xavierbasc/dm50/3d/render01.png

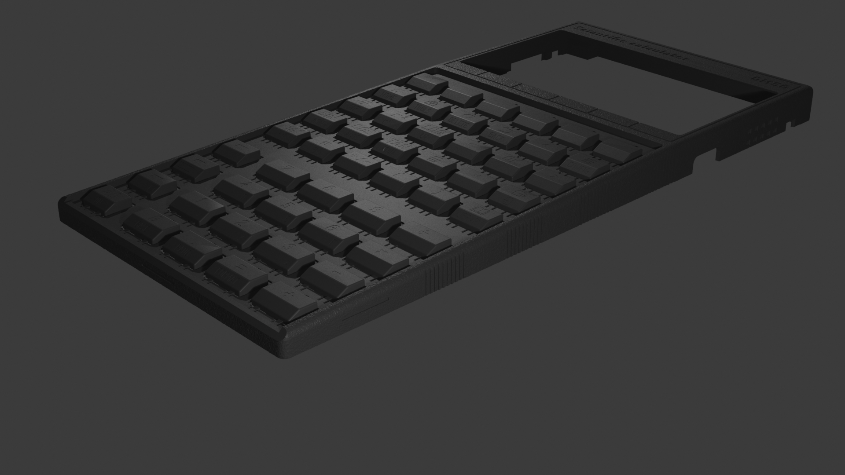
3d/render01.png
