xavierbasc/dm50/docs/img/AT25SF641.jpeg

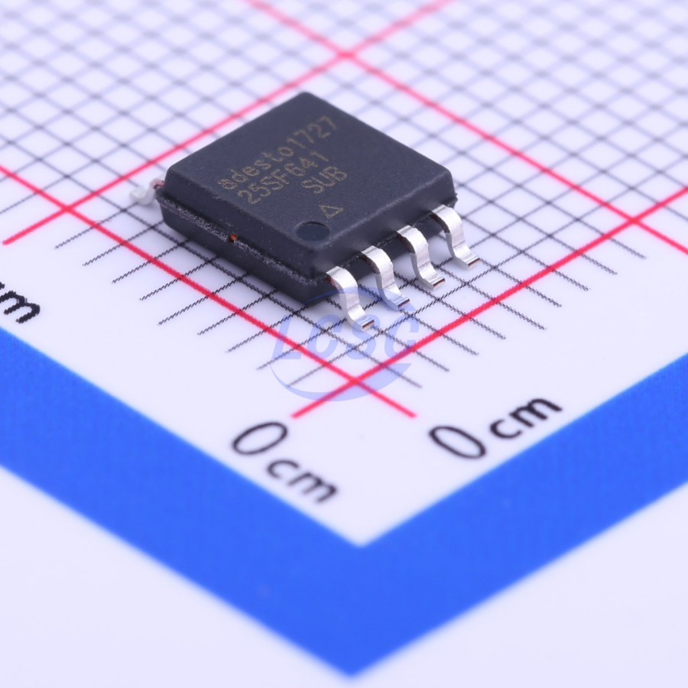
docs/img/AT25SF641.jpeg
