xavierbasc/dm50/docs/img/case3d.png

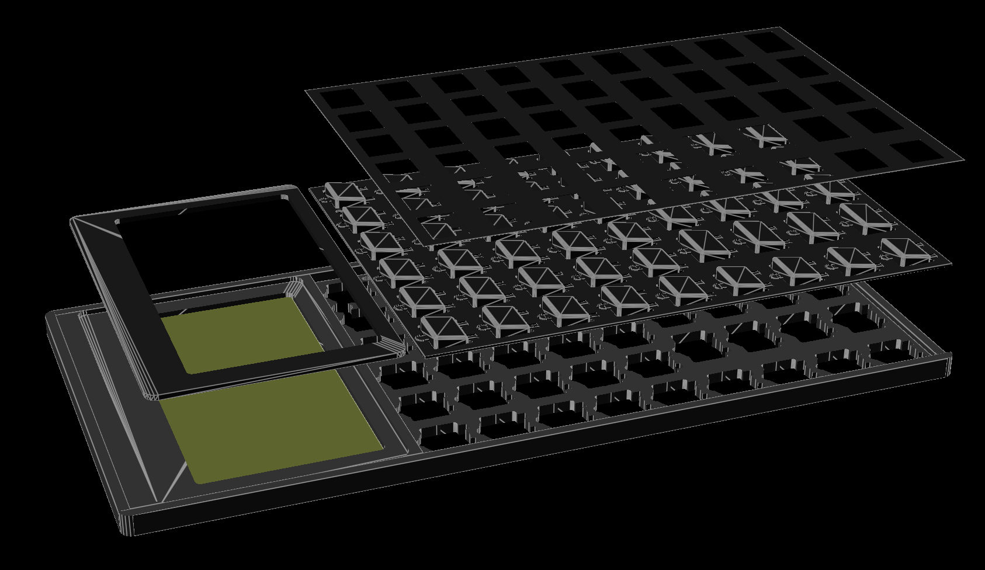
docs/img/case3d.png
