xavierbasc/dm50/docs/img/DM50_PCB.png

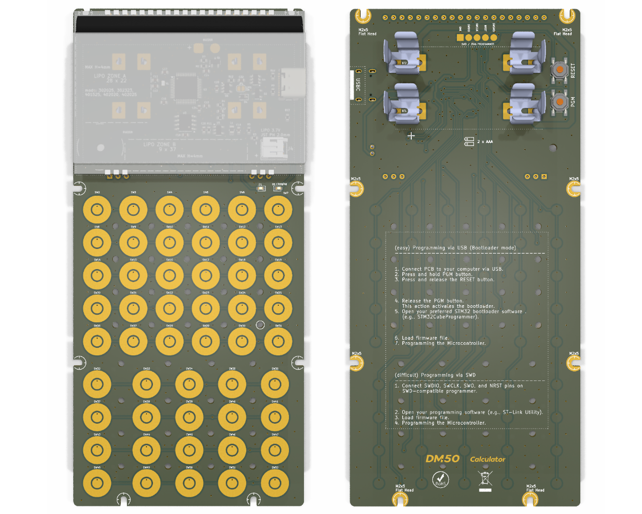
docs/img/DM50_PCB.png
