xavierbasc/dm50/docs/img/FFab.png

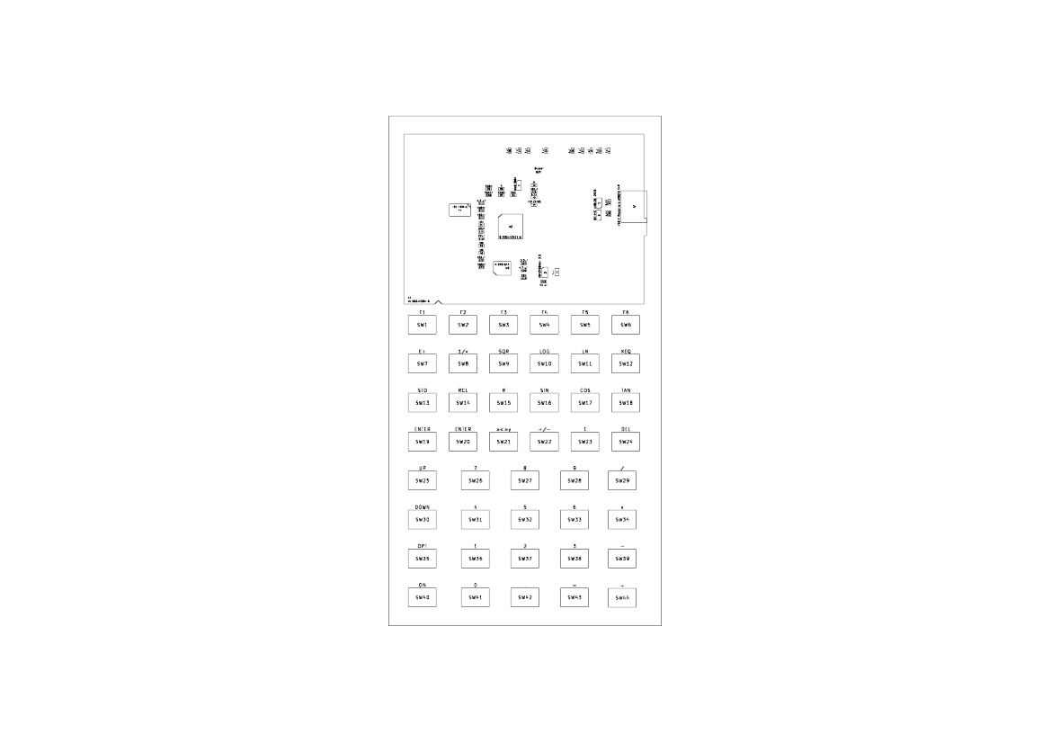
docs/img/FFab.png
