xavierbasc/dm50/docs/img/keyboard_b.png

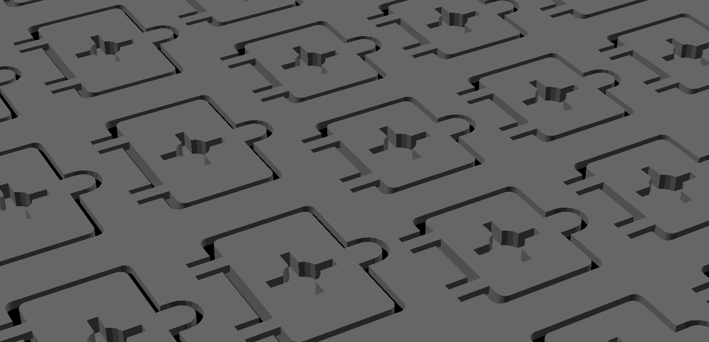
docs/img/keyboard_b.png
