xavierbasc/dm50/docs/img/PCB_3D_back.png

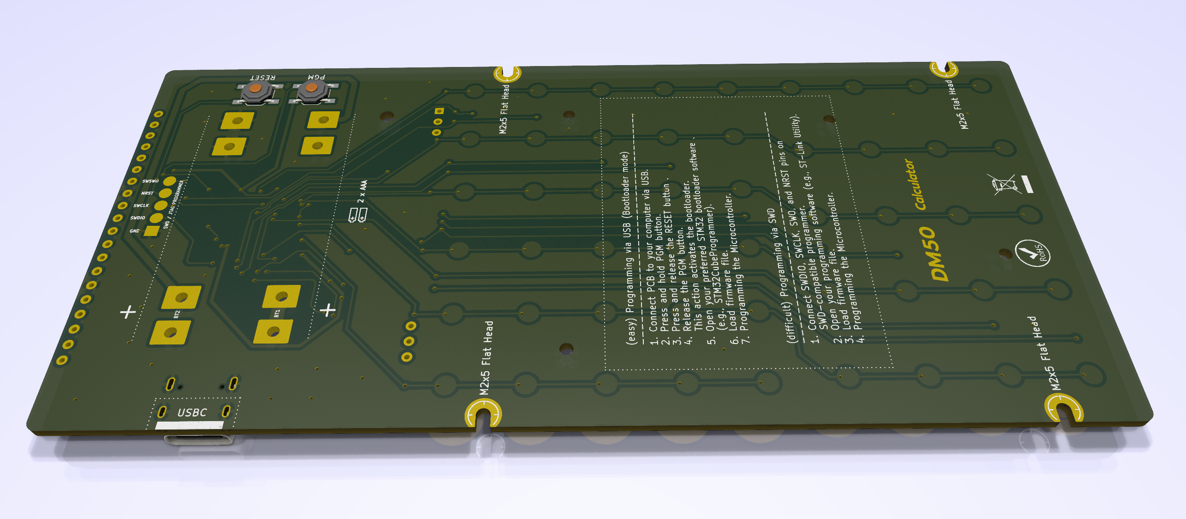
docs/img/PCB_3D_back.png
