xavierbasc/dm50/docs/pdf/PCB/FFab.pdf

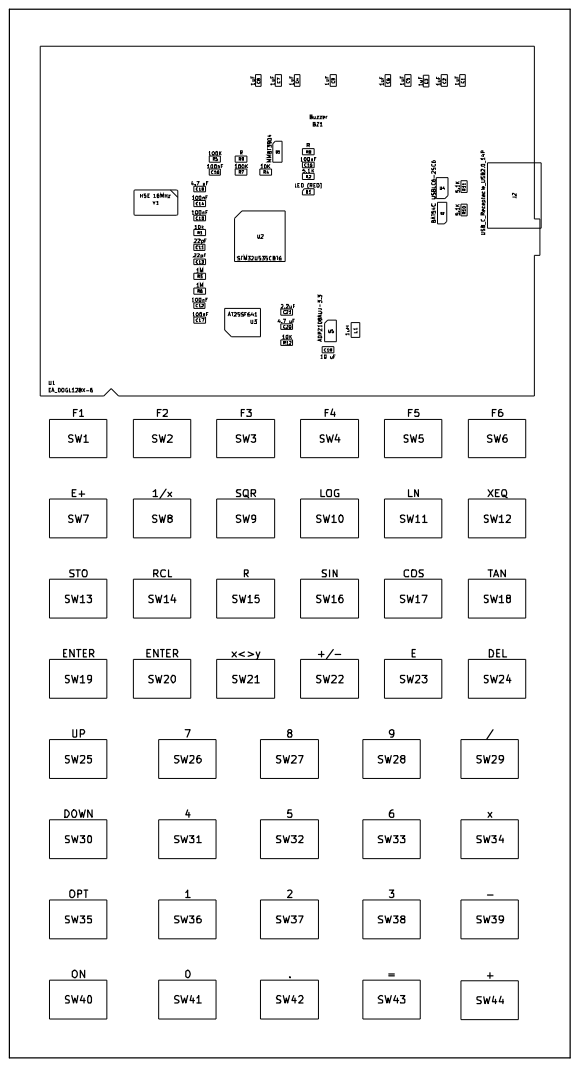
[picture p36: page 1]
